rheslip/Twisty-2-MIDIController/source/Twisty2_Rhythmicon/ClickEncoder.h

// ----------------------------------------------------------------------------
// Rotary Encoder Driver with Acceleration
// Supports Click, DoubleClick, Long Click
//
// (c) 2010 karl@pitrich.com
// (c) 2014 karl@pitrich.com
//
// Timer-based rotary encoder logic by Peter Dannegger
// http://www.mikrocontroller.net/articles/Drehgeber
// ----------------------------------------------------------------------------
// RH added button edge events which are needed sometimes Dec 2025

#ifndef __have__ClickEncoder_h__
#define __have__ClickEncoder_h__

// ----------------------------------------------------------------------------

//#include <stdint.h>
//#include <avr/io.h>
//#include <avr/interrupt.h>
//#include <avr/pgmspace.h>
#include "Arduino.h"

// ----------------------------------------------------------------------------

#define ENC_NORMAL        (1 << 1)   // use Peter Danneger's decoder
#define ENC_FLAKY         (1 << 2)   // use Table-based decoder

// ----------------------------------------------------------------------------

#ifndef ENC_DECODER
#  define ENC_DECODER     ENC_NORMAL
#endif

#if ENC_DECODER == ENC_FLAKY
#  ifndef ENC_HALFSTEP
#    define ENC_HALFSTEP  1        // use table for half step per default
#  endif
#endif

// ----------------------------------------------------------------------------

class ClickEncoder
{
public:
  typedef enum Button_e {  // these are a mix of states and events
    Open = 0,
    Closed,

    Pressed,
    Held,
    Released,

    Clicked,
    DoubleClicked

  } Button;

  typedef enum Button_ev { // these are events
    NoEvent = 0,
    ActiveEdge,
    InActiveEdge
  } ButtonEvent;

public:
  ClickEncoder(uint8_t A, uint8_t B, uint8_t BTN = -1,
               uint8_t stepsPerNotch = 1, bool active = LOW);

  void service(void);
  int16_t getValue(void);

#ifndef WITHOUT_BUTTON
public:
  Button getButton(void);
  ButtonEvent getButtonEvent(void);
#endif

#ifndef WITHOUT_BUTTON
public:
  void setDoubleClickEnabled(const bool d)
  {
    doubleClickEnabled = d;
  }

  const bool getDoubleClickEnabled()
  {
    return doubleClickEnabled;
  }
#endif

public:
  void setAccelerationEnabled(const bool &a)
  {
    accelerationEnabled = a;
    if (accelerationEnabled == false) {
      acceleration = 0;
    }
  }

  const bool getAccelerationEnabled()
  {
    return accelerationEnabled;
  }

private:
  const uint8_t pinA;
  const uint8_t pinB;
  const uint8_t pinBTN;
  const bool pinsActive;
  volatile int16_t delta;
  volatile int16_t last;
  uint8_t steps;
  volatile uint16_t acceleration;
  bool accelerationEnabled;
#if ENC_DECODER != ENC_NORMAL
  static const int8_t table[16];
#endif
#ifndef WITHOUT_BUTTON
  volatile Button button;
  volatile ButtonEvent event;
  bool edge=0;
  bool doubleClickEnabled;
  uint16_t keyDownTicks = 0;
  uint8_t doubleClickTicks = 0;
  unsigned long lastButtonCheck = 0;
#endif
};

// ----------------------------------------------------------------------------

#endif // __have__ClickEncoder_h__
