rheslip/Twisty-2-MIDIController/source/Twisty2/fileio.h

// Copyright 2023 Rich Heslip
//
// Author: Rich Heslip 
//
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
// See http://creativecommons.org/licenses/MIT/ for more information.
//
// -----------------------------------------------------------------------------


// file operations for Twisty 2
//  settings of encoders and switches saved and loaded in JSON format
// JSON allows adding features without breaking old settings
// using the LittleFFS filesystem in Pico Arduino 
// you have to set up an FFS partition in Arduino tools menu or file operations will fail

#define VERSION 100 // file format version in case it changes at some point

// save current settings to filesystem in JSON format

int16_t saveconfig(int16_t slot) {
  char filename[20];
  sprintf(filename,"slot%d.json",slot);

  if (LittleFS.exists(filename)) LittleFS.remove(filename); // delete exiting file

  File file = LittleFS.open(filename, "w");
  if (!file) {
    Serial.println("file open failed");
    return 0;
  }

  file.printf("{ \"Version\" : %d ,\n",VERSION);
  file.printf("\"page\" :  [\n");

  for (int16_t p=0;p<CONTROLLER_PAGES;++p) {
    file.printf("  { \"control\" : [ \n");
    for (int16_t c=0; c< NUMENCODERS;c++) {
    //  file.printf("  { \"control\" : [ {");
      file.printf("    { \"EncoderType\":%d,",controls[p].encoder[c].type);
      file.printf("\"EncoderChannel\":%d,",controls[p].encoder[c].channel);
      file.printf("\"EncoderCCNumber\":%d,",controls[p].encoder[c].ccnumber);
      file.printf("\"EncoderMinValue\":%d,",controls[p].encoder[c].minvalue);
      file.printf("\"EncoderMaxValue\":%d,",controls[p].encoder[c].maxvalue);
      file.printf("\"EncoderValue\":%d,",controls[p].encoder[c].value);
      file.printf("\"EncoderColorIndex\":%d,",controls[p].encoder[c].colorindex);
      file.printf("\"EncoderLabelIndex\":%d,",controls[p].encoder[c].labelindex);
      file.printf("\"SwitchMode\":%d,",controls[p].encswitch[c].mode);
      file.printf("\"SwitchType\":%d,",controls[p].encswitch[c].type);
      file.printf("\"SwitchChannel\":%d,",controls[p].encswitch[c].channel);
      file.printf("\"SwitchCC\":%d,",controls[p].encswitch[c].ccnumber);
      file.printf("\"SwitchMinValue\":%d,",controls[p].encswitch[c].minvalue);
      file.printf("\"SwitchMaxValue\":%d,",controls[p].encswitch[c].maxvalue);
      file.printf("\"SwitchValue\":%d,",controls[p].encswitch[c].value);
      file.printf("\"SwitchColorIndex\":%d,",controls[p].encswitch[c].colorindex);
      file.printf("\"SwitchLabelIndex\":%d",controls[p].encswitch[c].labelindex);
      if (c == (NUMENCODERS-1)) file.printf("}\n");
      else file.printf("},\n");
    }
    if (p == (CONTROLLER_PAGES-1)) file.printf("    ]\n  }\n");
    else file.printf("    ]\n  },\n");
  }
  file.printf("]\n}\n");
  file.close();
  return 1;
}


// read and deserialize JSON settings file

int16_t loadconfig(int16_t slot) {
  char filename[20];
  sprintf(filename,"slot%d.json",slot);

  File file = LittleFS.open(filename, "r");
  if (!file) {
    Serial.println("file open failed");
    return 0;
  }
  if (!file) {
    Serial.println("Failed to open file for reading");
    return 0;
  }

  // Allocate the JSON document 
  JsonDocument doc;

  // Deserialize JSON document from file
  DeserializationError error = deserializeJson(doc, file);

  file.close();

  if (error) {
    Serial.print(F("deserializeJson() failed: "));
    Serial.println(error.f_str());
    return 0;
  } else {
    // Data has been deserialized successfully, restore settings 

    for (int16_t p=0;p<CONTROLLER_PAGES;++p) {
      for (int16_t c=0; c< NUMENCODERS;c++) {
        controls[p].encoder[c].type=doc["page"][p]["control"][c]["EncoderMode"];
        controls[p].encoder[c].channel=doc["page"][p]["control"][c]["EncoderChannel"];
        controls[p].encoder[c].ccnumber=doc["page"][p]["control"][c]["EncoderCCNumber"];
        controls[p].encoder[c].minvalue=doc["page"][p]["control"][c]["EncoderMinValue"];
        controls[p].encoder[c].maxvalue=doc["page"][p]["control"][c]["EncoderMaxValue"];
        controls[p].encoder[c].value=doc["page"][p]["control"][c]["EncoderValue"];
        controls[p].encoder[c].colorindex=doc["page"][p]["control"][c]["EncoderColorIndex"];
        controls[p].encoder[c].labelindex=doc["page"][p]["control"][c]["EncoderLabelIndex"];
        controls[p].encswitch[c].mode=doc["page"][p]["control"][c]["SwitchMode"];
        controls[p].encswitch[c].type=doc["page"][p]["control"][c]["SwitchType"];
        controls[p].encswitch[c].channel=doc["page"][p]["control"][c]["SwitchChannel"];
        controls[p].encswitch[c].ccnumber=doc["page"][p]["control"][c]["SwitchCCNumber"];
        controls[p].encswitch[c].minvalue=doc["page"][p]["control"][c]["SwitchMinValue"];
        controls[p].encswitch[c].maxvalue=doc["page"][p]["control"][c]["SwitchMaxValue"];
        controls[p].encswitch[c].value=doc["page"][p]["control"][c]["SwitchValue"];
        controls[p].encswitch[c].colorindex=doc["page"][p]["control"][c]["SwitchColorIndex"];
        controls[p].encswitch[c].labelindex=doc["page"][p]["control"][c]["SwitchLabelIndex"];
      }
    }
  }
  return 1;
}

/*
// debug code - show files and contents
int16_t loadconfig(int16_t slot) {
  Dir dir = LittleFS.openDir("/");
  while (dir.next()) {
      Serial.println(dir.fileName());
      if(dir.fileSize()) {
          File file = dir.openFile("r");
          while(file.available()){
        // Read one byte at a time and print to Serial Monitor
            Serial.write(file.read());
          }
          file.close();
      }
      
  }
  return 1;
}
*/
